xioTechnologies/Human-Harp-Player/Firmware/Receive/Receive.c

/**
 * @file Receive.c
 * @author Seb Madgwick
 * @brief Application tasks and functions for receiving messages.
 */

//------------------------------------------------------------------------------
// Includes

#include "Encoder/Encoder.h"
#include "Imu/Imu.h"
#include "Send/Send.h"
#include "Timer/Timer.h"
#include "Uart/Uart1.h"

//------------------------------------------------------------------------------
// Functions

/**
 * @brief Do tasks.  This function should be called repeatedly within the main
 * program loop.
 */
void ReceiveDoTasks() {
    while (Uart1IsGetReady() > 0) {
        switch (Uart1GetChar()) {
            case 'f':
            case 'F':
                SendFirmwareVersion();
                TimerDelay(2000);
                break;
            case 'r':
            case 'R':
                asm("RESET");
                break;
            case 'z':
            case 'Z':
                EncoderZero();
                ImuZero();
                SendZero();
                break;
            default:
                break;
        }
    }
}

//------------------------------------------------------------------------------
// End of file
